Rooteq/quadro/description/meshes/cybergear_body.stl

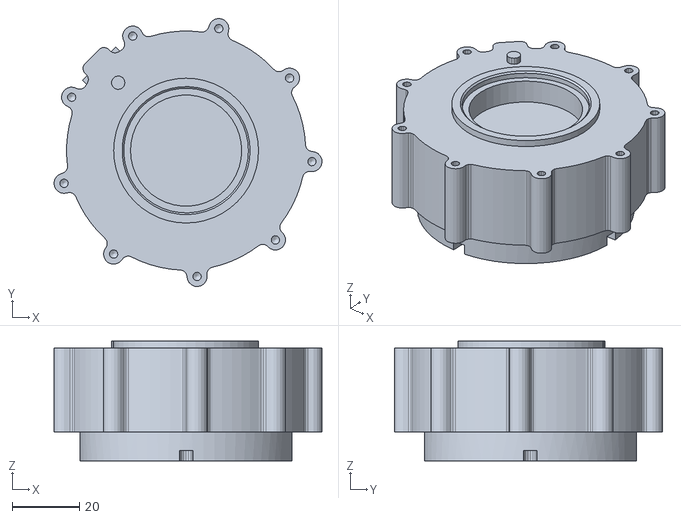
[picture p16: CAD file, 2025-02-20]
description/meshes/cybergear_body.stl
79.6 x 79.6 x 35.5
