Rooteq/quadro/description/assets/mid_clamp.stl

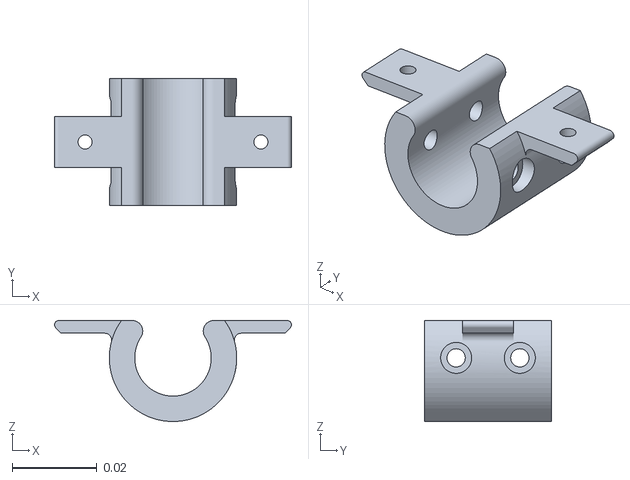
[picture p17: CAD file, 2025-12-01]
description/assets/mid_clamp.stl
0.0558 x 0.03 x 0.0238
