Rooteq/quadro/description/leg_assets/back_plate.stl

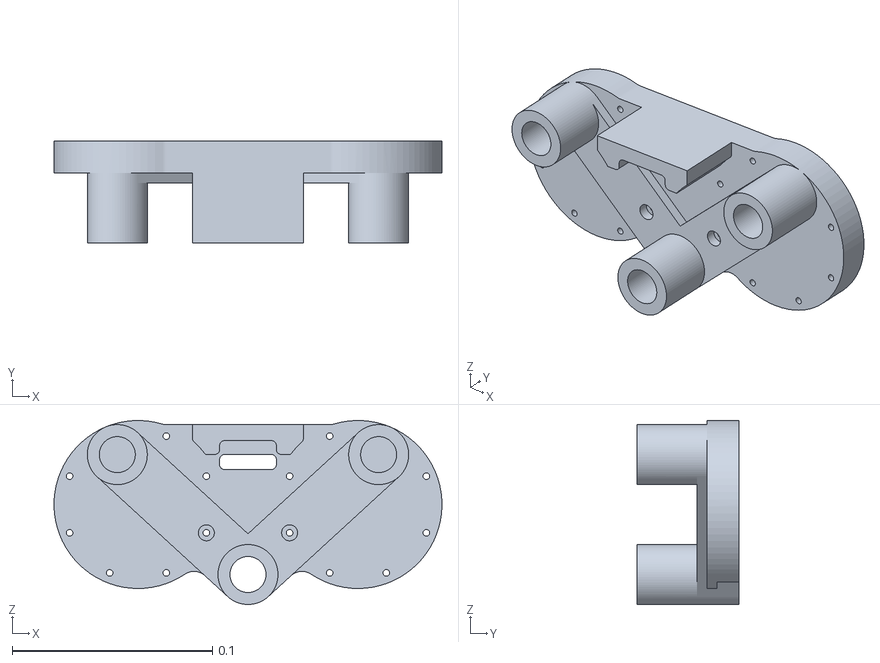
[picture p18: CAD file, 2025-07-25]
description/leg_assets/back_plate.stl
0.194 x 0.051 x 0.092
