Rooteq/quadro/description/meshes/cybergear_table.stl

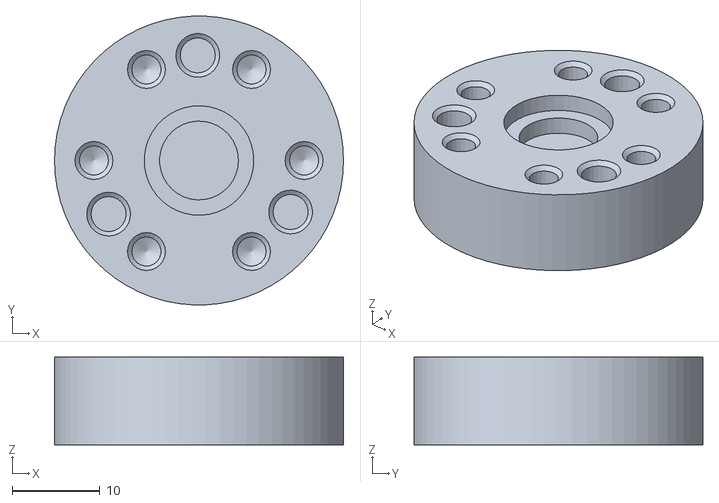
[picture p19: CAD file, 2025-02-20]
description/meshes/cybergear_table.stl
33.0 x 33.0 x 10.0
