Rooteq/quadro/description/assets/bot_pipe_half.stl

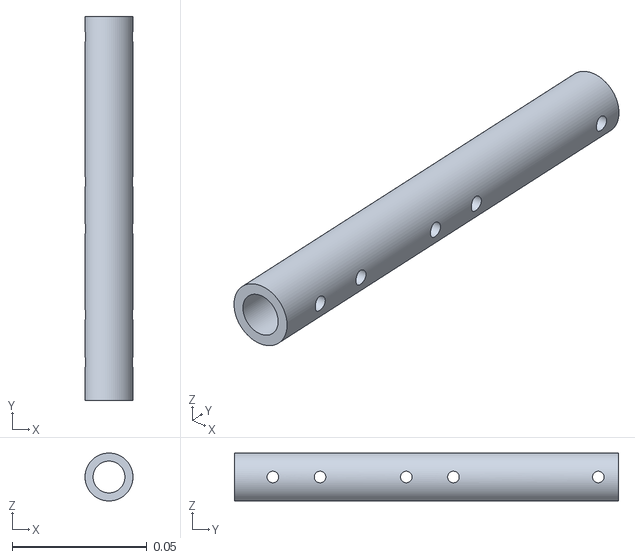
[picture p20: CAD file, 2025-12-01]
description/assets/bot_pipe_half.stl
0.0178 x 0.143 x 0.0178
