Rooteq/quadro/description/leg_assets/back_stop.stl

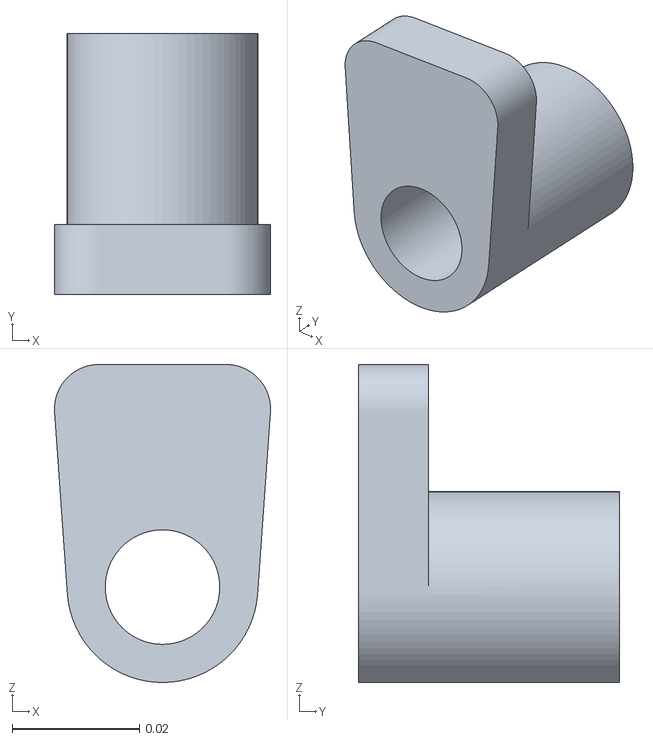
[picture p21: CAD file, 2025-07-25]
description/leg_assets/back_stop.stl
0.034 x 0.041 x 0.05
