Rooteq/quadro/description/assets/bot_l.stl

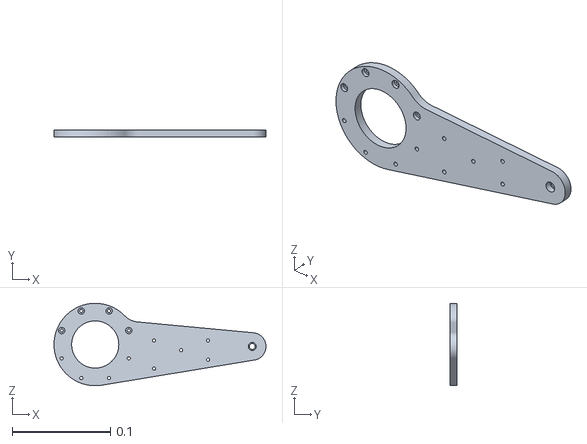
[picture p22: CAD file, 2025-12-01]
description/assets/bot_l.stl
0.216 x 0.007 x 0.084
