Rooteq/quadro/description/leg_assets/lin_top_l.stl

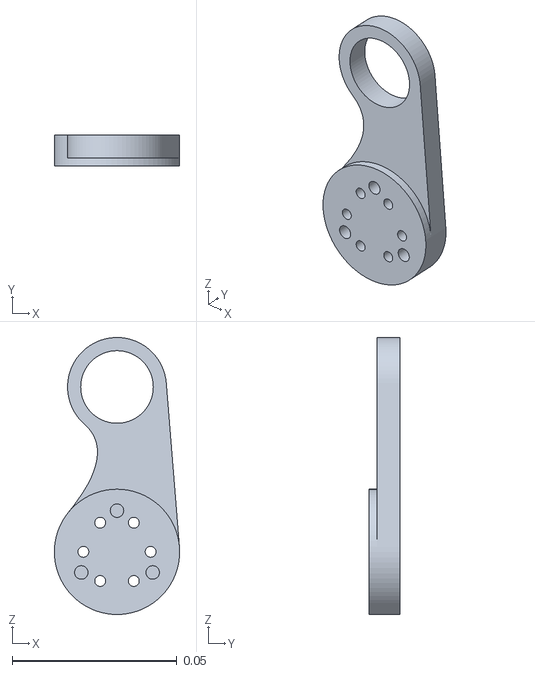
[picture p23: CAD file, 2025-07-25]
description/leg_assets/lin_top_l.stl
0.038 x 0.0095 x 0.084
