Rooteq/quadro/description/assets/top_l.stl

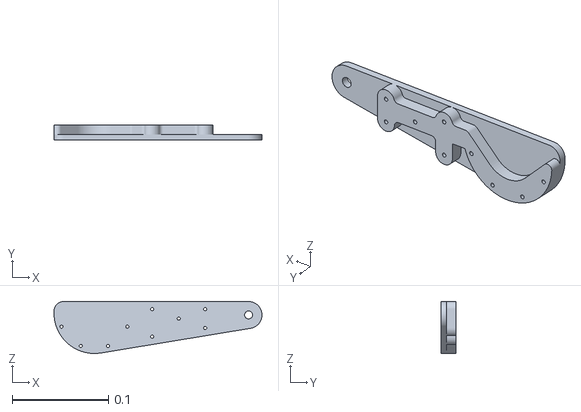
[picture p24: CAD file, 2025-12-01]
description/assets/top_l.stl
0.216 x 0.016 x 0.054
