Rooteq/quadro/description/leg_assets/lin_3_top_l.stl

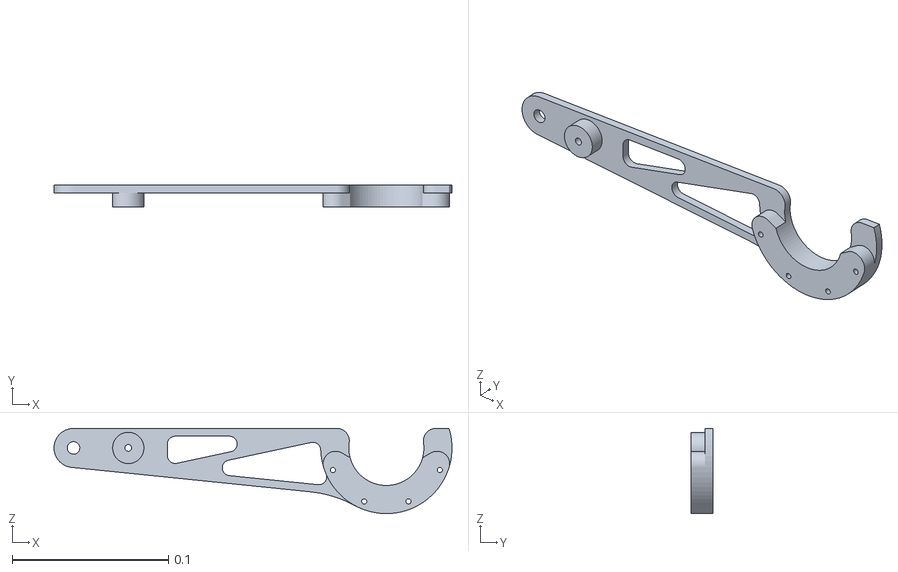
[picture p25: CAD file, 2025-07-25]
description/leg_assets/lin_3_top_l.stl
0.254 x 0.014 x 0.0545
