Rooteq/quadro/description/assets/r_pi.stl

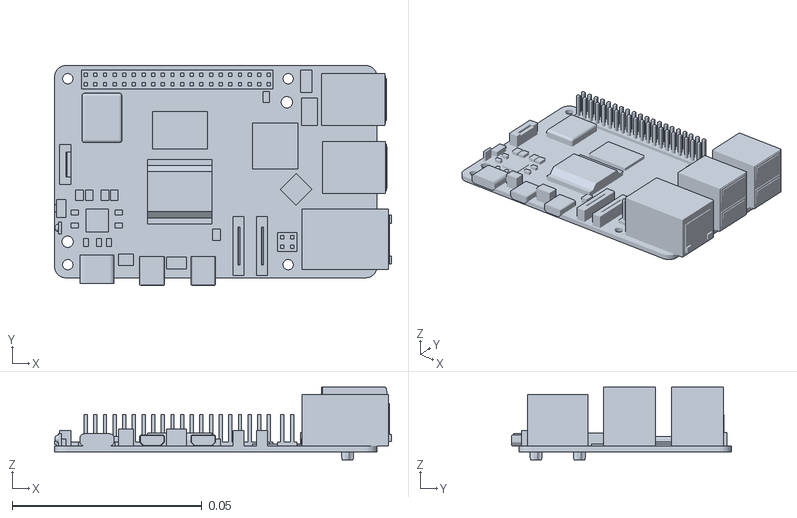
[picture p26: CAD file, 2025-12-01]
description/assets/r_pi.stl
0.0888 x 0.058 x 0.0192
