Rooteq/quadro/description/leg_assets/lin_1_support_bl.stl

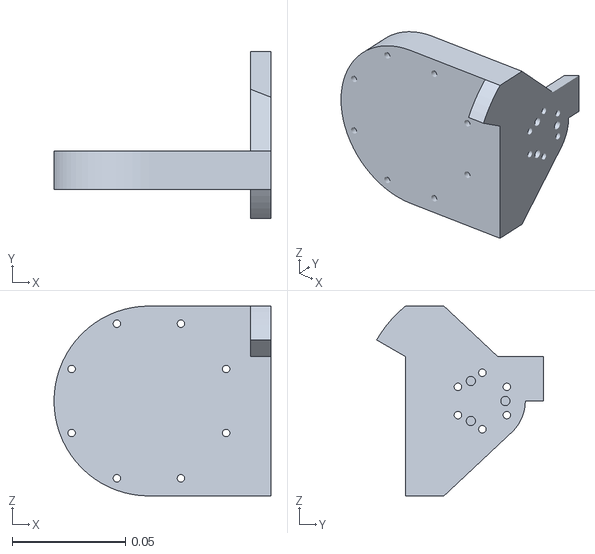
[picture p27: CAD file, 2025-07-25]
description/leg_assets/lin_1_support_bl.stl
0.096 x 0.0738 x 0.084
