Rooteq/quadro/description/assets/side_pipe.stl

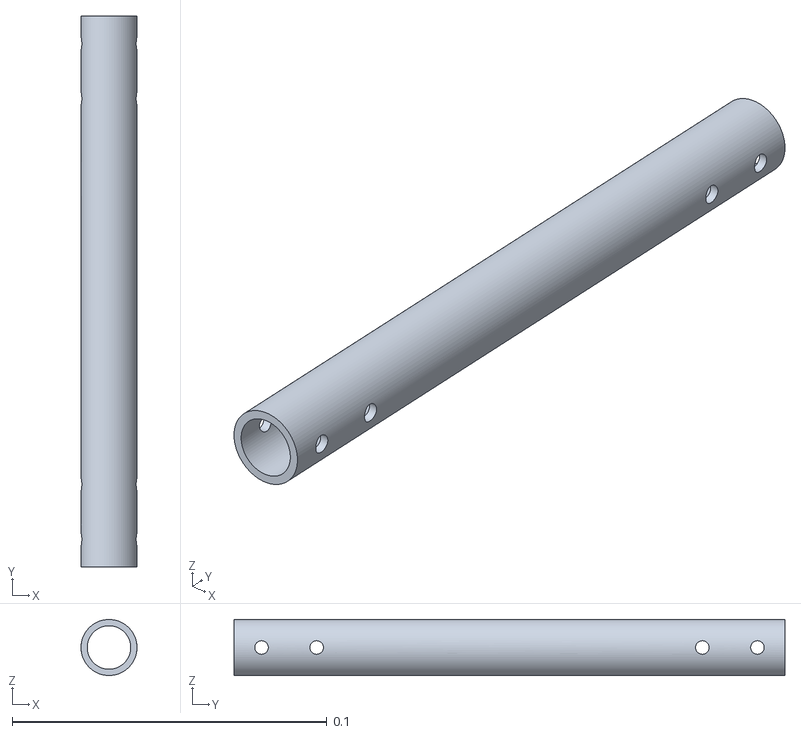
[picture p28: CAD file, 2025-12-01]
description/assets/side_pipe.stl
0.0178 x 0.175 x 0.0178
