Rooteq/quadro/description/assets/back_plate.stl

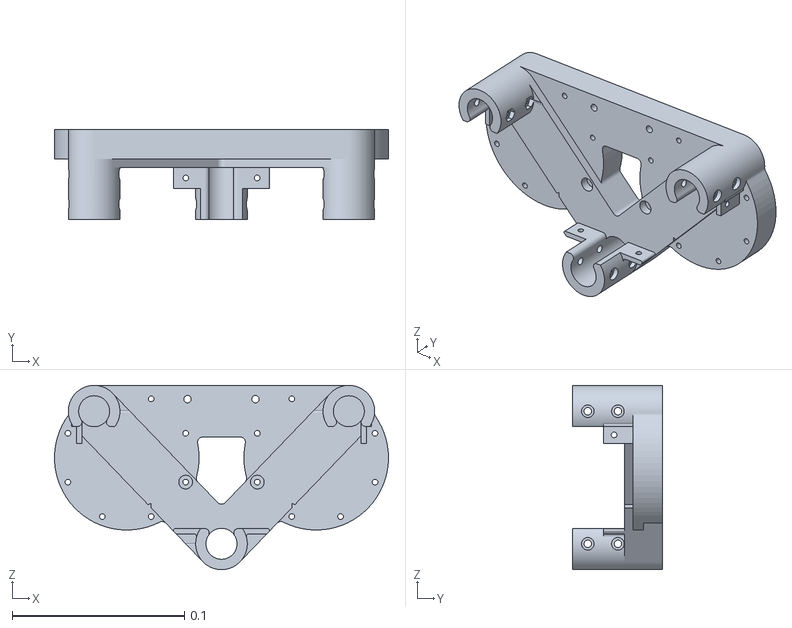
[picture p29: CAD file, 2025-12-01]
description/assets/back_plate.stl
0.194 x 0.052 x 0.107
