Rooteq/quadro/description/assets/pierdolnik.stl

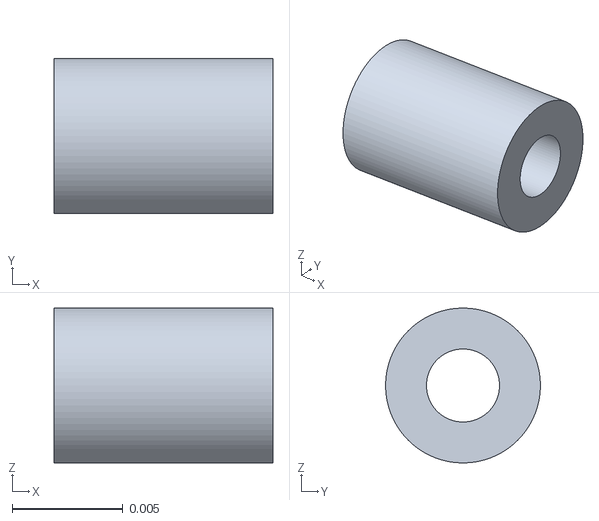
[picture p30: CAD file, 2025-12-01]
description/assets/pierdolnik.stl
0.0099 x 0.007 x 0.007
