Rooteq/quadro/description/assets/l4_l.stl

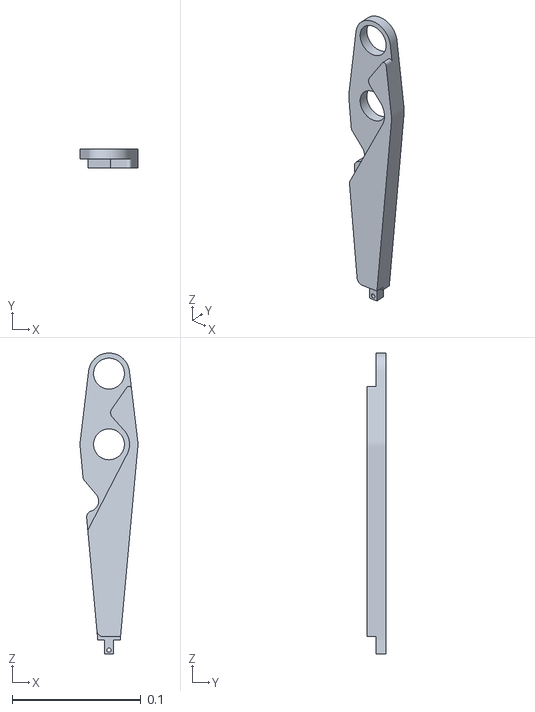
[picture p31: CAD file, 2025-12-01]
description/assets/l4_l.stl
0.045 x 0.015 x 0.234
