Rooteq/quadro/description/leg_assets/bearing.stl

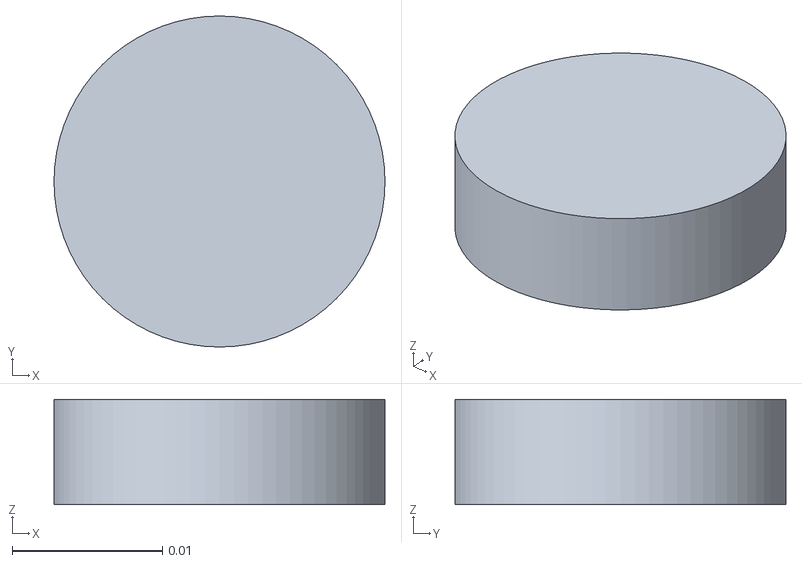
[picture p32: CAD file, 2025-07-10]
description/leg_assets/bearing.stl
0.022 x 0.022 x 0.007
