Rooteq/quadro/description/assets/mid_r.stl

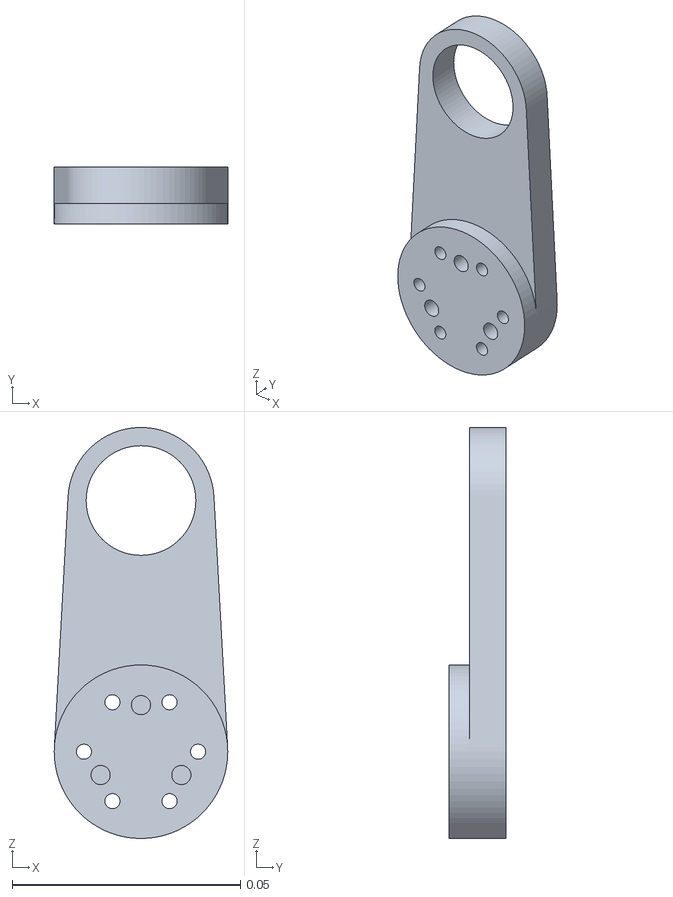
[picture p33: CAD file, 2025-12-01]
description/assets/mid_r.stl
0.038 x 0.0125 x 0.09
