Rooteq/quadro/description/assets/side_cover.stl

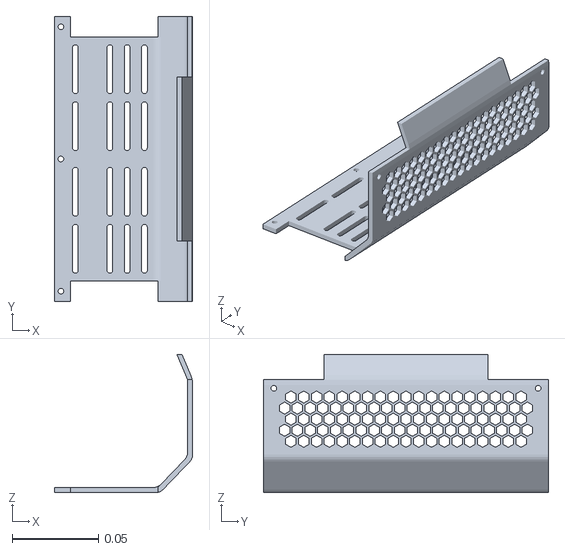
[picture p34: CAD file, 2025-12-01]
description/assets/side_cover.stl
0.0802 x 0.165 x 0.0801
