Rooteq/quadro/description/leg_assets/shaft.stl

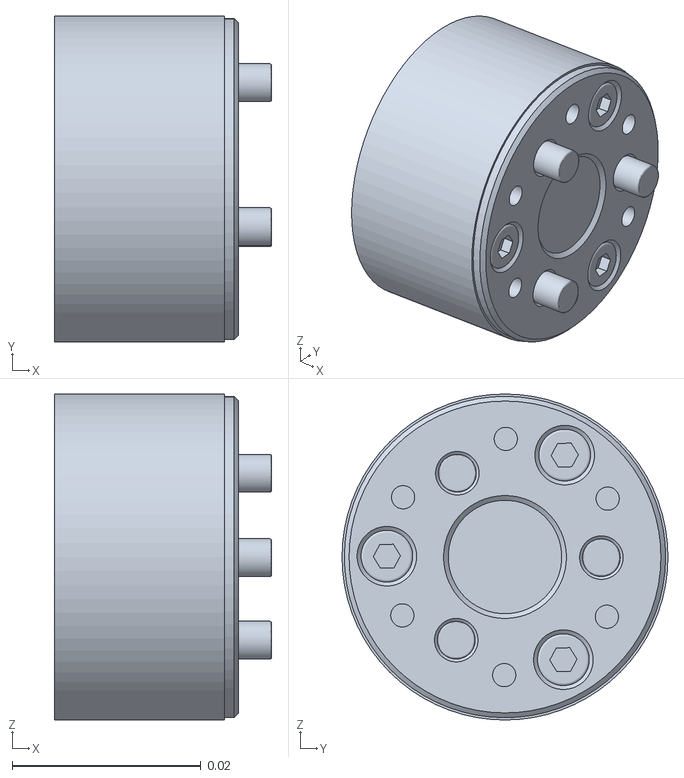
[picture p35: CAD file, 2025-07-09]
description/leg_assets/shaft.stl
0.023 x 0.0345 x 0.0345
