Rooteq/quadro/description/assets/lin_2_bl.stl

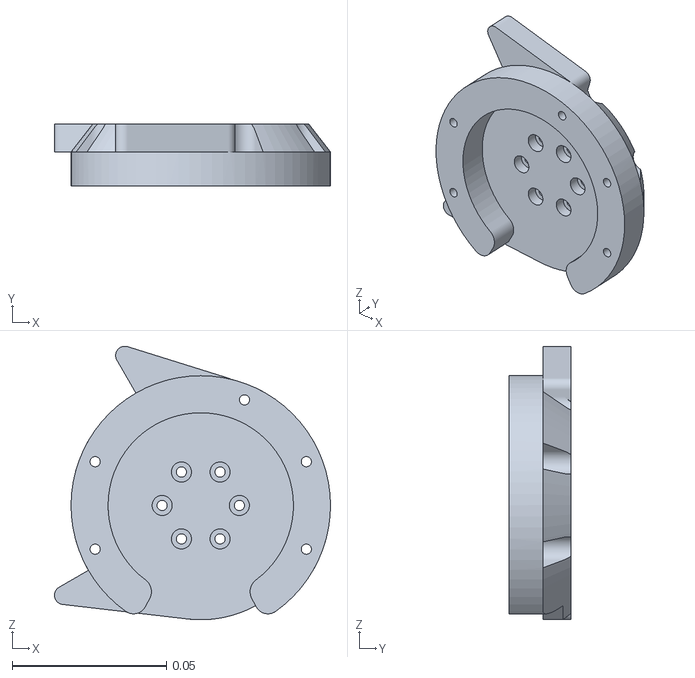
[picture p36: CAD file, 2025-12-01]
description/assets/lin_2_bl.stl
0.0893 x 0.02 x 0.0885
