Rooteq/quadro/description/assets/back_stop.stl

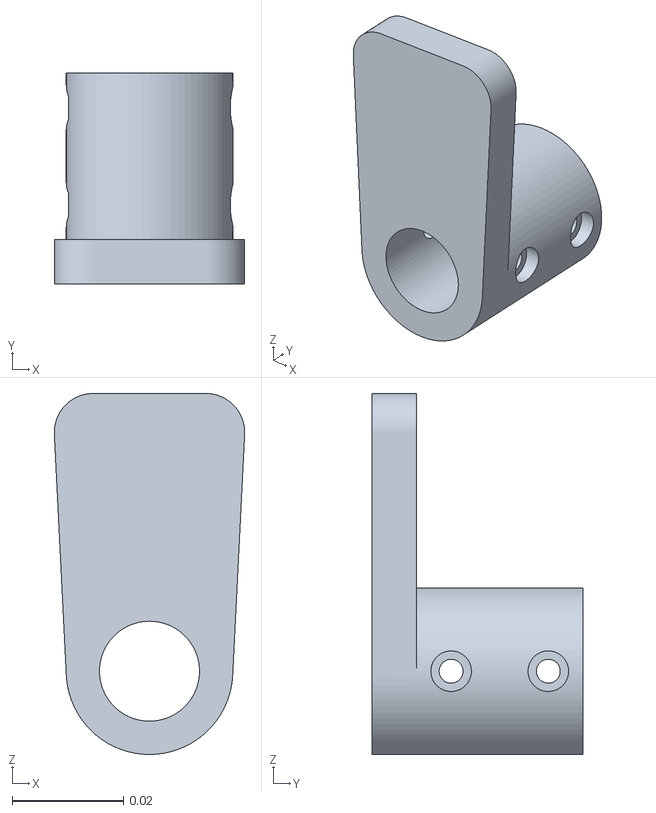
[picture p37: CAD file, 2025-12-01]
description/assets/back_stop.stl
0.0343 x 0.038 x 0.065
