Rooteq/quadro/description/assets/battery.stl

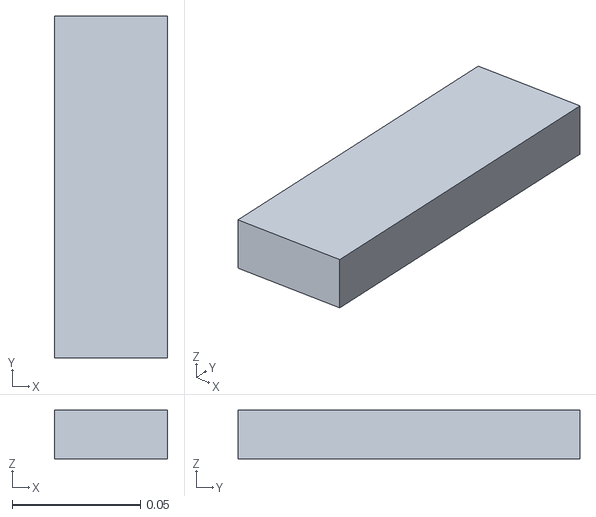
[picture p38: CAD file, 2025-07-25]
description/assets/battery.stl
0.044 x 0.133 x 0.019
