Rooteq/quadro/description/robot.xacro

<?xml version="1.0" ?>
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
<robot name="robot" xmlns:xacro="http://www.ros.org/wiki/xacro">
<xacro:arg name="sim_mode" default="false"/>

<xacro:if value="$(arg sim_mode)">
  <xacro:include filename="$(find quadro)/description/robot.gazebo" />
</xacro:if>

<xacro:unless value="$(arg sim_mode)">
  <xacro:include filename="$(find quadro)/description/ros2_control.xacro" />
</xacro:unless>
  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

  <link name="back_plate">
    <inertial>
      <origin xyz="-0.139034 0.00943483 -0.0243213" rpy="0 0 0"/>
      <mass value="2.38325"/>
      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
    </inertial>
    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
  </link>
  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
  <link name="shaft">
    <inertial>
      <origin xyz="-0.00743033 0.00365203 -0.0538481" rpy="0 0 0"/>
      <mass value="0.500834"/>
      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
    </inertial>
    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
  </link>
  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
  <link name="shaft_2">
    <inertial>
      <origin xyz="0.0106548 -0.00501565 -0.0435875" rpy="0 0 0"/>
      <mass value="0.551476"/>
      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
    </inertial>
    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
  </link>
  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
  <link name="shaft_3">
    <inertial>
      <origin xyz="0.00299793 0.00329395 -0.0125923" rpy="0 0 0"/>
      <mass value="0.140118"/>
      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
    </inertial>
    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
  </link>
  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
  <joint name="br_m3_s3" type="revolute">
    <origin xyz="2.77556e-17 8.04912e-16 -0.0485" rpy="6.66134e-16 8.32667e-17 -0.349066"/>
    <parent link="shaft_2"/>
    <child link="shaft_3"/>
    <axis xyz="0 0 1"/>
    <limit effort="10" velocity="12" lower="-3.14" upper="3.14"/>
    <joint_properties friction="0.5"/>
    <mimic joint="br_l4_l3" multiplier="1.0"/>
  </joint>
  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
  <link name="lin_4_r">
    <inertial>
      <origin xyz="-0.000162389 0.0733841 -0.0035" rpy="0 0 0"/>
      <mass value="0.0813924"/>
      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
    </inertial>
    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
  </link>
  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
  <joint name="br_l4_l3" type="revolute">
    <origin xyz="0.187939 -0.068404 -0.0705" rpy="1.85962e-15 3.88578e-16 2.00713"/>
    <parent link="shaft_2"/>
    <child link="lin_4_r"/>
    <axis xyz="0 0 1"/>
    <limit effort="10" velocity="12" lower="-3.14" upper="3.14"/>
    <joint_properties friction="0.5"/>
  </joint>
  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
  <joint name="br_m2_s2" type="revolute">
    <origin xyz="-0.00606218 0.0035 -0.0735" rpy="-2.61799 1.5708 0"/>
    <parent link="shaft"/>
    <child link="shaft_2"/>
    <axis xyz="0 0 1"/>
    <limit effort="10" velocity="12" lower="-3.14" upper="3.14"/>
    <joint_properties friction="0.5"/>
  </joint>
  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
  <joint name="br_m1_s1" type="revolute">
    <origin xyz="-0.194034 0.120935 -0.023441" rpy="-1.5708 -5.95406e-36 -3.14159"/>
    <parent link="back_plate"/>
    <child link="shaft"/>
    <axis xyz="0 0 1"/>
    <limit effort="10" velocity="12" lower="-3.14" upper="3.14"/>
    <joint_properties friction="0.5"/>
  </joint>
  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
  <link name="shaft_4">
    <inertial>
      <origin xyz="0.00743033 0.00365203 -0.0535667" rpy="0 0 0"/>
      <mass value="0.500834"/>
      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
    </inertial>
    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
  </link>
  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
  <link name="shaft_5">
    <inertial>
      <origin xyz="0.00646492 0.00964883 -0.0435875" rpy="0 0 0"/>
      <mass value="0.551476"/>
      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
    </inertial>
    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
  </link>
  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
  <link name="shaft_6">
    <inertial>
      <origin xyz="-0.00299792 0.00329395 -0.0125923" rpy="0 0 0"/>
      <mass value="0.140118"/>
      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
    </inertial>
    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
  </link>
  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
  <joint name="bl_m3_s3" type="revolute">
    <origin xyz="3.05311e-16 -1.38778e-17 -0.0485" rpy="2.60902e-15 3.66374e-15 -2.26893"/>
    <parent link="shaft_5"/>
    <child link="shaft_6"/>
    <axis xyz="0 0 1"/>
    <limit effort="10" velocity="12" lower="-3.14" upper="3.14"/>
    <joint_properties friction="0.5"/>
    <mimic joint="bl_l4_l3" multiplier="1.0"/>
  </joint>
  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
  <link name="lin_4_l">
    <inertial>
      <origin xyz="-0.000162393 -0.0733841 -0.0035" rpy="0 0 0"/>
      <mass value="0.0813924"/>
      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
    </inertial>
    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
  </link>
  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
  <joint name="bl_l4_l3" type="revolute">
    <origin xyz="0.128558 0.153209 -0.0705" rpy="1.41553e-15 -2.55351e-15 -1.48353"/>
    <parent link="shaft_5"/>
    <child link="lin_4_l"/>
    <axis xyz="0 0 1"/>
    <limit effort="10" velocity="12" lower="-3.14" upper="3.14"/>
    <joint_properties friction="0.5"/>
  </joint>
  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
  <joint name="bl_m2_s2" type="revolute">
    <origin xyz="0.00606218 0.0035 -0.0735" rpy="-1.5708 1.0472 -1.0472"/>
    <parent link="shaft_4"/>
    <child link="shaft_5"/>
    <axis xyz="0 0 1"/>
    <limit effort="10" velocity="12" lower="-3.14" upper="3.14"/>
    <joint_properties friction="0.5"/>
  </joint>
  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
  <joint name="bl_m1_s1" type="revolute">
    <origin xyz="-0.0840337 0.120935 -0.023441" rpy="-1.5708 -5.95406e-36 -3.14159"/>
    <parent link="back_plate"/>
    <child link="shaft_4"/>
    <axis xyz="0 0 1"/>
    <limit effort="10" velocity="12" lower="-3.14" upper="3.14"/>
    <joint_properties friction="0.5"/>
  </joint>
  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
  <link name="shaft_7">
    <inertial>
      <origin xyz="-0.00738234 -0.00373514 -0.0535667" rpy="0 0 0"/>
      <mass value="0.500834"/>
      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
    </inertial>
    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
  </link>
  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
  <link name="shaft_8">
    <inertial>
      <origin xyz="0.0110758 -0.00536086 -0.0435639" rpy="0 0 0"/>
      <mass value="0.55218"/>
      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
    </inertial>
    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
  </link>
  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
  <link name="shaft_9">
    <inertial>
      <origin xyz="0.00299793 0.00329395 -0.0125923" rpy="0 0 0"/>
      <mass value="0.140118"/>
      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
    </inertial>
    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
  </link>
  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
  <joint name="fr_m3_s3" type="revolute">
    <origin xyz="-7.21645e-16 5.96745e-16 -0.0485" rpy="-7.77156e-16 -4.71845e-16 -0.349066"/>
    <parent link="shaft_8"/>
    <child link="shaft_9"/>
    <axis xyz="0 0 1"/>
    <limit effort="10" velocity="12" lower="-3.14" upper="3.14"/>
    <joint_properties friction="0.5"/>
    <mimic joint="fr_l4_l3" multiplier="1.0"/>
  </joint>
  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
  <link name="lin_4_r_2">
    <inertial>
      <origin xyz="-0.000162389 0.0733841 -0.0035" rpy="0 0 0"/>
      <mass value="0.0813924"/>
      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
    </inertial>
    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
  </link>
  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
  <joint name="fr_l4_l3" type="revolute">
    <origin xyz="0.187939 -0.068404 -0.0705" rpy="5.82867e-16 -2.22045e-16 2.00713"/>
    <parent link="shaft_8"/>
    <child link="lin_4_r_2"/>
    <axis xyz="0 0 1"/>
    <limit effort="10" velocity="12" lower="-3.14" upper="3.14"/>
    <joint_properties friction="0.5"/>
  </joint>
  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
  <joint name="fr_m2_s2" type="revolute">
    <origin xyz="-0.00606218 -0.0035 -0.0735" rpy="0.523599 -1.5708 0"/>
    <parent link="shaft_7"/>
    <child link="shaft_8"/>
    <axis xyz="0 0 1"/>
    <limit effort="10" velocity="12" lower="-3.14" upper="3.14"/>
    <joint_properties friction="0.5"/>
  </joint>
  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
  <joint name="fr_m1_s1" type="revolute">
    <origin xyz="-0.194034 -0.102065 -0.023441" rpy="1.5708 -0 -3.14159"/>
    <parent link="back_plate"/>
    <child link="shaft_7"/>
    <axis xyz="0 0 1"/>
    <limit effort="10" velocity="12" lower="-3.14" upper="3.14"/>
    <joint_properties friction="0.5"/>
  </joint>
  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
  <link name="motor">
    <inertial>
      <origin xyz="0.00738234 -0.00373514 -0.0538481" rpy="0 0 0"/>
      <mass value="0.500834"/>
      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
    </inertial>
    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
  </link>
  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
  <link name="motor_2">
    <inertial>
      <origin xyz="-0.0108445 -0.00546873 -0.0435639" rpy="0 0 0"/>
      <mass value="0.55218"/>
      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
    </inertial>
    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
  </link>
  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
  <link name="shaft_10">
    <inertial>
      <origin xyz="-0.00299792 0.00329395 -0.0125923" rpy="0 0 0"/>
      <mass value="0.140118"/>
      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
    </inertial>
    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
  </link>
  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
  <joint name="fl_m3_s3" type="revolute">
    <origin xyz="6.93889e-16 5.44703e-16 -0.0485" rpy="-4.996e-15 -3.71925e-15 0.349066"/>
    <parent link="motor_2"/>
    <child link="shaft_10"/>
    <axis xyz="0 0 1"/>
    <limit effort="10" velocity="12" lower="-3.14" upper="3.14"/>
    <joint_properties friction="0.5"/>
    <mimic joint="fl_l4_l3" multiplier="1.0"/>
  </joint>
  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
  <link name="lin_4_l_2">
    <inertial>
      <origin xyz="-0.000162393 -0.0733841 -0.0035" rpy="0 0 0"/>
      <mass value="0.0813924"/>
      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
    </inertial>
    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
  </link>
  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
  <joint name="fl_l4_l3" type="revolute">
    <origin xyz="-0.187939 -0.068404 -0.0705" rpy="2.04559e-14 4.95715e-14 1.13446"/>
    <parent link="motor_2"/>
    <child link="lin_4_l_2"/>
    <axis xyz="0 0 1"/>
    <limit effort="10" velocity="12" lower="-3.14" upper="3.14"/>
    <joint_properties friction="0.5"/>
  </joint>
  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
  <joint name="fl_m2_s2" type="revolute">
    <origin xyz="0.00606218 -0.0035 -0.0735" rpy="0.523599 1.5708 0"/>
    <parent link="motor"/>
    <child link="motor_2"/>
    <axis xyz="0 0 1"/>
    <limit effort="10" velocity="12" lower="-3.14" upper="3.14"/>
    <joint_properties friction="0.5"/>
  </joint>
  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
  <joint name="fl_m1_s1" type="revolute">
    <origin xyz="-0.0840337 -0.102065 -0.023441" rpy="1.5708 -0 -3.14159"/>
    <parent link="back_plate"/>
    <child link="motor"/>
    <axis xyz="0 0 1"/>
    <limit effort="10" velocity="12" lower="-3.14" upper="3.14"/>
    <joint_properties friction="0.5"/>
  </joint>
</robot>
