Rooteq/quadro/description/robot_full_urdf.urdf

<?xml version="1.0" ?>
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
<robot name="robot">
  <ros2_control name="CybergearActuators" type="actuator">
    <hardware>
      <plugin>quadro/CybergearActuator</plugin>
      <param name="can_interface">can0</param>
      <param name="timeout_sec">3.0</param>
      <param name="use_bus_time">false</param>
      <param name="interval_sec">0.5</param>
      <param name="primary_id">0</param>
    </hardware>
    <joint name="br_m1_s1">
      <command_interface name="position">
      </command_interface>
      <state_interface name="position"/>
      <state_interface name="velocity"/>
    </joint>
    <joint name="br_m2_s2">
      <command_interface name="position">
      </command_interface>
      <state_interface name="position"/>
      <state_interface name="velocity"/>
    </joint>
    <joint name="br_m3_s3">
      <command_interface name="position">
      </command_interface>
      <state_interface name="position"/>
      <state_interface name="velocity"/>
    </joint>
    <joint name="bl_m1_s1">
      <command_interface name="position">
      </command_interface>
      <state_interface name="position"/>
      <state_interface name="velocity"/>
    </joint>
    <joint name="bl_m2_s2">
      <command_interface name="position">
      </command_interface>
      <state_interface name="position"/>
      <state_interface name="velocity"/>
    </joint>
    <joint name="bl_m3_s3">
      <command_interface name="position">
      </command_interface>
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
    <parent link="shaft_5"/>
    <child link="shaft_6"/>
    <axis xyz="0 0 1"/>
    <limit effort="10" lower="-3.14" upper="3.14" velocity="12"/>
    <joint_properties friction="0.5"/>
    <mimic joint="bl_l4_l3" multiplier="1.0"/>
  </joint>
  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
  <link name="lin_4_l">
    <inertial>
      <origin rpy="0 0 0" xyz="-0.000162393 -0.0733841 -0.0035"/>
      <mass value="0.0813924"/>
      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
    </inertial>
    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
  </link>
  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
  <joint name="bl_l4_l3" type="revolute">
    <origin rpy="1.41553e-15 -2.55351e-15 -1.48353" xyz="0.128558 0.153209 -0.0705"/>
    <parent link="shaft_5"/>
    <child link="lin_4_l"/>
    <axis xyz="0 0 1"/>
    <limit effort="10" lower="-3.14" upper="3.14" velocity="12"/>
    <joint_properties friction="0.5"/>
  </joint>
  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
  <joint name="bl_m2_s2" type="revolute">
    <origin rpy="-1.5708 1.0472 -1.0472" xyz="0.00606218 0.0035 -0.0735"/>
    <parent link="shaft_4"/>
    <child link="shaft_5"/>
    <axis xyz="0 0 1"/>
    <limit effort="10" lower="-3.14" upper="3.14" velocity="12"/>
    <joint_properties friction="0.5"/>
  </joint>
  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
  <joint name="bl_m1_s1" type="revolute">
    <origin rpy="-1.5708 -5.95406e-36 -3.14159" xyz="-0.0840337 0.120935 -0.023441"/>
    <parent link="back_plate"/>
    <child link="shaft_4"/>
    <axis xyz="0 0 1"/>
    <limit effort="10" lower="-3.14" upper="3.14" velocity="12"/>
    <joint_properties friction="0.5"/>
  </joint>
  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
  <link name="shaft_7">
    <inertial>
      <origin rpy="0 0 0" xyz="-0.00738234 -0.00373514 -0.0535667"/>
      <mass value="0.500834"/>
      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
    </inertial>
    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
  </link>
  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
  <link name="shaft_8">
    <inertial>
      <origin rpy="0 0 0" xyz="0.0110758 -0.00536086 -0.0435639"/>
      <mass value="0.55218"/>
      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
    </inertial>
    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
  </link>
  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
  <link name="shaft_9">
    <inertial>
      <origin rpy="0 0 0" xyz="0.00299793 0.00329395 -0.0125923"/>
      <mass value="0.140118"/>
      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
    </inertial>
    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
  </link>
  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
  <joint name="fr_m3_s3" type="revolute">
    <origin rpy="-7.77156e-16 -4.71845e-16 -0.349066" xyz="-7.21645e-16 5.96745e-16 -0.0485"/>
    <parent link="shaft_8"/>
    <child link="shaft_9"/>
    <axis xyz="0 0 1"/>
    <limit effort="10" lower="-3.14" upper="3.14" velocity="12"/>
    <joint_properties friction="0.5"/>
    <mimic joint="fr_l4_l3" multiplier="1.0"/>
  </joint>
  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
  <link name="lin_4_r_2">
    <inertial>
      <origin rpy="0 0 0" xyz="-0.000162389 0.0733841 -0.0035"/>
      <mass value="0.0813924"/>
      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
    </inertial>
    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
  </link>
  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
  <joint name="fr_l4_l3" type="revolute">
    <origin rpy="5.82867e-16 -2.22045e-16 2.00713" xyz="0.187939 -0.068404 -0.0705"/>
    <parent link="shaft_8"/>
    <child link="lin_4_r_2"/>
    <axis xyz="0 0 1"/>
    <limit effort="10" lower="-3.14" upper="3.14" velocity="12"/>
    <joint_properties friction="0.5"/>
  </joint>
  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
  <joint name="fr_m2_s2" type="revolute">
    <origin rpy="0.523599 -1.5708 0" xyz="-0.00606218 -0.0035 -0.0735"/>
    <parent link="shaft_7"/>
    <child link="shaft_8"/>
    <axis xyz="0 0 1"/>
    <limit effort="10" lower="-3.14" upper="3.14" velocity="12"/>
    <joint_properties friction="0.5"/>
  </joint>
  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
  <joint name="fr_m1_s1" type="revolute">
    <origin rpy="1.5708 -0 -3.14159" xyz="-0.194034 -0.102065 -0.023441"/>
    <parent link="back_plate"/>
    <child link="shaft_7"/>
    <axis xyz="0 0 1"/>
    <limit effort="10" lower="-3.14" upper="3.14" velocity="12"/>
    <joint_properties friction="0.5"/>
  </joint>
  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
  <link name="motor">
    <inertial>
      <origin rpy="0 0 0" xyz="0.00738234 -0.00373514 -0.0538481"/>
      <mass value="0.500834"/>
      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
    </inertial>
    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
  </link>
  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
  <link name="motor_2">
    <inertial>
      <origin rpy="0 0 0" xyz="-0.0108445 -0.00546873 -0.0435639"/>
      <mass value="0.55218"/>
      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
    </inertial>
    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
  </link>
  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
  <link name="shaft_10">
    <inertial>
      <origin rpy="0 0 0" xyz="-0.00299792 0.00329395 -0.0125923"/>
      <mass value="0.140118"/>
      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
    </inertial>
    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
  </link>
  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
  <joint name="fl_m3_s3" type="revolute">
    <origin rpy="-4.996e-15 -3.71925e-15 0.349066" xyz="6.93889e-16 5.44703e-16 -0.0485"/>
    <parent link="motor_2"/>
    <child link="shaft_10"/>
    <axis xyz="0 0 1"/>
    <limit effort="10" lower="-3.14" upper="3.14" velocity="12"/>
    <joint_properties friction="0.5"/>
    <mimic joint="fl_l4_l3" multiplier="1.0"/>
  </joint>
  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
  <link name="lin_4_l_2">
    <inertial>
      <origin rpy="0 0 0" xyz="-0.000162393 -0.0733841 -0.0035"/>
      <mass value="0.0813924"/>
      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
    </inertial>
    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
  </link>
  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
  <joint name="fl_l4_l3" type="revolute">
    <origin rpy="2.04559e-14 4.95715e-14 1.13446" xyz="-0.187939 -0.068404 -0.0705"/>
    <parent link="motor_2"/>
    <child link="lin_4_l_2"/>
    <axis xyz="0 0 1"/>
    <limit effort="10" lower="-3.14" upper="3.14" velocity="12"/>
    <joint_properties friction="0.5"/>
  </joint>
  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
  <joint name="fl_m2_s2" type="revolute">
    <origin rpy="0.523599 1.5708 0" xyz="0.00606218 -0.0035 -0.0735"/>
    <parent link="motor"/>
    <child link="motor_2"/>
    <axis xyz="0 0 1"/>
    <limit effort="10" lower="-3.14" upper="3.14" velocity="12"/>
    <joint_properties friction="0.5"/>
  </joint>
  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
  <joint name="fl_m1_s1" type="revolute">
    <origin rpy="1.5708 -0 -3.14159" xyz="-0.0840337 -0.102065 -0.023441"/>
    <parent link="back_plate"/>
    <child link="motor"/>
    <axis xyz="0 0 1"/>
    <limit effort="10" lower="-3.14" upper="3.14" velocity="12"/>
    <joint_properties friction="0.5"/>
  </joint>
</robot>
